janmannsbart23/OBDShiftIndicator/Code/ESP32/OBDShiftIndicatorFirmware/src/DShiftModes.hpp

#pragma once

#include "FastLED.h"

CRGB shiftLightMode1[8][13] = {
    {CRGB::Black, CRGB::Black, CRGB::Black, CRGB::Black, CRGB::Black, CRGB::Black, CRGB::Black, CRGB::Black, CRGB::Black, CRGB::Black, CRGB::Black, CRGB::Black, CRGB::Black},
    {CRGB::Green, CRGB::Black, CRGB::Black, CRGB::Black, CRGB::Black, CRGB::Black, CRGB::Black, CRGB::Black, CRGB::Black, CRGB::Black, CRGB::Black, CRGB::Black, CRGB::Green},
    {CRGB::Green, CRGB::Green, CRGB::Black, CRGB::Black, CRGB::Black, CRGB::Black, CRGB::Black, CRGB::Black, CRGB::Black, CRGB::Black, CRGB::Black, CRGB::Green, CRGB::Green},
    {CRGB::Green, CRGB::Green, CRGB::Green, CRGB::Black, CRGB::Black, CRGB::Black, CRGB::Black, CRGB::Black, CRGB::Black, CRGB::Black, CRGB::Green, CRGB::Green, CRGB::Green},
    {CRGB::Green, CRGB::Green, CRGB::Green, CRGB::Red, CRGB::Black, CRGB::Black, CRGB::Black, CRGB::Black, CRGB::Black, CRGB::Red, CRGB::Green, CRGB::Green, CRGB::Green},
    {CRGB::Green, CRGB::Green, CRGB::Green, CRGB::Red, CRGB::Red, CRGB::Black, CRGB::Black, CRGB::Black, CRGB::Red, CRGB::Red, CRGB::Green, CRGB::Green, CRGB::Green},
    {CRGB::Green, CRGB::Green, CRGB::Green, CRGB::Red, CRGB::Red, CRGB::Blue, CRGB::Black, CRGB::Blue, CRGB::Red, CRGB::Red, CRGB::Green, CRGB::Green, CRGB::Green},
    {CRGB::Green, CRGB::Green, CRGB::Green, CRGB::Red, CRGB::Red, CRGB::Blue, CRGB::Blue, CRGB::Blue, CRGB::Red, CRGB::Red, CRGB::Green, CRGB::Green, CRGB::Green}};
